mr258876/Project-Puncher/Project_HolePuncher/src/PuncherMotors.cpp

#include "PuncherMotors.h"

MotorController *controller_X = NULL;
MotorController *controller_Y = NULL;
MotorController *controller_Z = NULL;

PositionSensor *sensor_X = NULL;
PositionSensor *sensor_Y = NULL;
PositionSensor *sensor_Z = NULL;
