mr258876/Project-Puncher/Project_HolePuncher/include/PuncherSchedulerAbst.h

#ifndef _PUNCHERSCHEDULERABST_H_
#define _PUNCHERSCHEDULERABST_H_

#include "PuncherSchedulerTyping.h"
#include "PuncherEvents.h"
#include <time.h>

class PuncherSchedulerInterface
{

public:
    virtual int start_workload() = 0;  // handle by queue
    virtual int pause_workload() = 0;  // handle by queue
    virtual int delete_workload() = 0; // handle by queue
    virtual int data_transmit_mode(bool transmit_mode) = 0;
    virtual int feed_paper_mode(bool feed_paper_mode) = 0;
    virtual int add_hole(scheduler_hole_t &h) = 0;
    /* Note: y in mcode is actually Z axis! */
    virtual int add_hold_mcode(int x, int y, int z) = 0;

    virtual int feed_paper(int gear, bool slow_mode) = 0;
    virtual int util_move_X(int dir, bool use_zeroing_conf) = 0; // handle by queue
    virtual int util_move_Y(int dir, bool use_zeroing_conf) = 0; // handle by queue
    virtual int read_sg_result(int axis) = 0;                    // handle by queue
    virtual int start_auto_zeroing(int axis) = 0;                // handle by queue
    virtual int start_encoder_calibrate(int axis) = 0;           // handle by queue

    virtual unsigned int set_status(unsigned int status_code) = 0;
    virtual unsigned int get_status() = 0;
    virtual time_t get_ETA() = 0;
    virtual void set_setting_value(puncher_event_setting_change_t *evt) = 0; // handle by queue
    virtual void get_setting_values(void *ui) = 0;
    virtual void get_status(void *ui) = 0;
};

#endif
