mr258876/Project-Puncher/Project_HolePuncher/include/PuncherSemaphore.h

#ifndef _PUNCHERSEMAPHORE_H_
#define _PUNCHERSEMAPHORE_H_

#include <freertos/FreeRTOS.h>
#include <freertos/semphr.h>

extern SemaphoreHandle_t I2C0Mutex;
extern SemaphoreHandle_t I2C1Mutex;
extern SemaphoreHandle_t SPI2Mutex;
extern SemaphoreHandle_t SPI3Mutex;
extern SemaphoreHandle_t *LCDMutexptr;
extern SemaphoreHandle_t LVGLMutex;
extern SemaphoreHandle_t UART0Mutex;
extern SemaphoreHandle_t UART1Mutex;
extern SemaphoreHandle_t UART2Mutex;
extern SemaphoreHandle_t *DUARTMutex;

#endif  // _PUNCHERSEMAPHORE_H_
