mr258876/Project-Puncher/Project_HolePuncher/src/ui/i18n/lv_i18n.c

#include "./lv_i18n.h"


////////////////////////////////////////////////////////////////////////////////
// Define plural operands
// http://unicode.org/reports/tr35/tr35-numbers.html#Operands

// Integer version, simplified

#define UNUSED(x) (void)(x)

static inline uint32_t op_n(int32_t val) { return (uint32_t)(val < 0 ? -val : val); }
static inline uint32_t op_i(uint32_t val) { return val; }
// always zero, when decimal part not exists.
static inline uint32_t op_v(uint32_t val) { UNUSED(val); return 0;}
static inline uint32_t op_w(uint32_t val) { UNUSED(val); return 0; }
static inline uint32_t op_f(uint32_t val) { UNUSED(val); return 0; }
static inline uint32_t op_t(uint32_t val) { UNUSED(val); return 0; }

static lv_i18n_phrase_t en_us_singulars[] = {
    {"Operational Speed (mm/s)", "Operational\nSpeed (mm/s)"},
    {"_length_type_options", "Diameter\nPerimeter"},
    {"Operational Current (mA)", "Operational\nCurrent (mA)"},
    {"_idle_behavior_options", "Keep Current\nReduce Current\nCut Power"},
    {"Auto Zeroing", "Auto\nZeroing"},
    {"Auto Zeroing on Boot", "Auto Zeroing\non Boot"},
    {"Reverse Zeroing Direction", "Reverse\nZeroing Dir."},
    {"Zeroing Torch Threshold", "Zeroing Torch\nThreshold"},
    {"Zeroing Speed (mm/s)", "Zeroing Speed\n(mm/s)"},
    {"Zeroing Position (mm)", "Zeroing Position\n(mm)"},
    {"Move Axis", "Move\nAxis"},
    {"SG Result", "SG Result: -1"},
    {"_sg_result_fmt", "SG Result: %d"},
    {"_move_axis_speed_options", "Operational\nZeroing"},
    {"_motor_voltage_options", "5V\n9V\n12V\n15V\n20V"},
    {"_language_options", "English\n简体中文"},
    {"Move Target Beats", "Move\nto Target"},
    {"Measured Residual (mm)", "Measured\nResidual (mm)"},
    {"Punch Depth (mm)", "Punch Depth\n(mm)"},
    {"_encoder_type_options", "AS5600"},
    {"Auto Calibrate", "Auto\nCalibrate"},
    {"_version", "Firmware Version\n%s"},
    {"_about_page_author", "@mr258876\n2023-2024\nPlease star this project on Github!"},
    {"_tips_1", "tips: You could send mission by USB, Wi-Fi or Bluetooth."},
    {"_driver_err_template", "Driver error on axis %s"},
    {"_motor_err_template", "Motor error on axis %s"},
    {"_power_err_template", "Failed to acquire votage."},
    {"_driver_err_template_tips", "Driver error on axis %s. Please check driver installation."},
    {"_motor_err_template_tips", "Motor error on axis %s. Please check cable connections."},
    {"_power_err_template_tips", "Failed to acquire votage. Please check compatibility of your power supply."},
    {NULL, NULL} // End mark
};



static uint8_t en_us_plural_fn(int32_t num)
{
    uint32_t n = op_n(num); UNUSED(n);
    uint32_t i = op_i(n); UNUSED(i);
    uint32_t v = op_v(n); UNUSED(v);

    if ((i == 1 && v == 0)) return LV_I18N_PLURAL_TYPE_ONE;
    return LV_I18N_PLURAL_TYPE_OTHER;
}

static const lv_i18n_lang_t en_us_lang = {
    .locale_name = "en-US",
    .singulars = en_us_singulars,

    .locale_plural_fn = en_us_plural_fn
};

static lv_i18n_phrase_t zh_cn_singulars[] = {
    {"Status", "状态"},
    {"ETA", "预计剩余时间"},
    {"Feed", "进纸"},
    {"Slow", "慢速"},
    {"Setting", "设置"},
    {"Info", "信息"},
    {"Warning", "警告"},
    {"Error", "错误"},
    {"Error Occured", "有错误发生"},
    {"Back", "返回"},
    {"About", "关于"},
    {"STOP", "停止"},
    {"Connectivity", "连接"},
    {"Motors", "电机"},
    {"Display", "显示"},
    {"Disp.", "显示"},
    {"Others", "其他"},
    {"Brightness", "亮度"},
    {"BLE", "蓝牙"},
    {"X Axis", "X轴"},
    {"Y Axis", "Y轴"},
    {"Z Axis", "Z轴"},
    {"Mechanical", "机械"},
    {"Lead Length (mm)", "导程长度(mm)"},
    {"Operational Speed (mm/s)", "运行速度(mm/s)"},
    {"Length Type", "长度类型"},
    {"_length_type_options", "直径\n周长"},
    {"Reverse Axis", "反转方向"},
    {"Electrical", "电气"},
    {"Operational Current (mA)", "运行电流(mA)"},
    {"Idle Behavior", "空闲行为"},
    {"_idle_behavior_options", "保持电流\n减小电流\n切断电源"},
    {"Sleep Current (mA)", "睡眠电流(mA)"},
    {"Zeroing", "归位"},
    {"Auto Zeroing", "自动归位"},
    {"Auto Zeroing on Boot", "开机自动归位"},
    {"Reverse Zeroing Direction", "反转归位方向"},
    {"Zeroing Torch Threshold", "归位力矩阈值"},
    {"Zeroing Current (mA)", "归位电流(mA)"},
    {"Zeroing Speed (mm/s)", "归位速度(mm/s)"},
    {"Zeroing Position (mm)", "归位后位置(mm)"},
    {"Execute", "执行"},
    {"Utility", "微调工具"},
    {"Move Axis", "启动电机"},
    {"SG Result", "力矩读数: -1"},
    {"_sg_result_fmt", "力矩读数: %d"},
    {"Speed Type", "速度类型"},
    {"_move_axis_speed_options", "按运行设置\n按归位设置"},
    {"Power", "供电"},
    {"Voltage", "电压"},
    {"Motor Voltage", "电机电压"},
    {"Screen", "屏幕"},
    {"System", "系统"},
    {"Language", "语言"},
    {"_language_options", "English\n简体中文"},
    {"Mcode Tickrate", "Mcode 每小节tick数"},
    {"Calibration", "校准"},
    {"Target Beats", "目标拍数"},
    {"Move Target Beats", "移动至\n目标拍数"},
    {"Measured Beats", "测量拍数"},
    {"Measured Residual (mm)", "测量残差(mm)"},
    {"Punch Depth (mm)", "打孔深度(mm)"},
    {"Idle", "空闲"},
    {"Ready", "就绪"},
    {"Receiving Data", "正在接收数据"},
    {"Encoder", "编码器"},
    {"Use Encoder", "启用编码器"},
    {"Encoder Type", "编码器类型"},
    {"_encoder_type_options", "AS5600"},
    {"Auto Calibrate", "自动校准"},
    {"Please Wait", "请稍候"},
    {"Axis Zeroing...", "正在自动归位..."},
    {"Transmitting Data...", "正在传输数据..."},
    {"_version", "固件版本\n%s"},
    {"_about_page_author", "@mr258876\n2023-2024\n请在 Github 上为该项目点 Star !"},
    {"_tips_1", "提示: 您可以通过USB, 无线网络或蓝牙传输作业任务。"},
    {"_driver_err_template", "%s 轴驱动器异常"},
    {"_motor_err_template", "%s 轴电机异常"},
    {"_power_err_template", "请求电压失败"},
    {"_driver_err_template_tips", "%s 轴驱动器异常。请检查驱动器是否已正确安装。"},
    {"_motor_err_template_tips", "%s 轴电机异常。请检查电机线缆是否断开。"},
    {"_power_err_template_tips", "请求电压失败。请检查电源兼容性。"},
    {"_driver_err_template_cpp", "轴驱动器异常"},
    {"_motor_err_template_cpp", "轴电机异常"},
    {"_driver_err_template_cpp_tips", "轴驱动器异常。请检查驱动器是否已正确安装。"},
    {"_motor_err_template_cpp_tips", "轴电机异常。请检查电机线缆是否断开。"},
    {NULL, NULL} // End mark
};



static uint8_t zh_cn_plural_fn(int32_t num)
{



    return LV_I18N_PLURAL_TYPE_OTHER;
}

static const lv_i18n_lang_t zh_cn_lang = {
    .locale_name = "zh-CN",
    .singulars = zh_cn_singulars,

    .locale_plural_fn = zh_cn_plural_fn
};

const lv_i18n_language_pack_t lv_i18n_language_pack[] = {
    &en_us_lang,
    &zh_cn_lang,
    NULL // End mark
};

////////////////////////////////////////////////////////////////////////////////


// Internal state
static const lv_i18n_language_pack_t * current_lang_pack;
static const lv_i18n_lang_t * current_lang;


/**
 * Reset internal state. For testing.
 */
void __lv_i18n_reset(void)
{
    current_lang_pack = NULL;
    current_lang = NULL;
}

/**
 * Set the languages for internationalization
 * @param langs pointer to the array of languages. (Last element has to be `NULL`)
 */
int lv_i18n_init(const lv_i18n_language_pack_t * langs)
{
    if(langs == NULL) return -1;
    if(langs[0] == NULL) return -1;

    current_lang_pack = langs;
    current_lang = langs[0];     /*Automatically select the first language*/
    return 0;
}

/**
 * Change the localization (language)
 * @param l_name name of the translation locale to use. E.g. "en-GB"
 */
int lv_i18n_set_locale(const char * l_name)
{
    if(current_lang_pack == NULL) return -1;

    uint16_t i;

    for(i = 0; current_lang_pack[i] != NULL; i++) {
        // Found -> finish
        if(strcmp(current_lang_pack[i]->locale_name, l_name) == 0) {
            current_lang = current_lang_pack[i];
            return 0;
        }
    }

    return -1;
}


static const char * __lv_i18n_get_text_core(lv_i18n_phrase_t * trans, const char * msg_id)
{
    uint16_t i;
    for(i = 0; trans[i].msg_id != NULL; i++) {
        if(strcmp(trans[i].msg_id, msg_id) == 0) {
            /*The msg_id has found. Check the translation*/
            if(trans[i].translation) return trans[i].translation;
        }
    }

    return NULL;
}


/**
 * Get the translation from a message ID
 * @param msg_id message ID
 * @return the translation of `msg_id` on the set local
 */
const char * lv_i18n_get_text(const char * msg_id)
{
    if(current_lang == NULL) return msg_id;

    const lv_i18n_lang_t * lang = current_lang;
    const void * txt;

    // Search in current locale
    if(lang->singulars != NULL) {
        txt = __lv_i18n_get_text_core(lang->singulars, msg_id);
        if (txt != NULL) return txt;
    }

    // Try to fallback
    if(lang == current_lang_pack[0]) return msg_id;
    lang = current_lang_pack[0];

    // Repeat search for default locale
    if(lang->singulars != NULL) {
        txt = __lv_i18n_get_text_core(lang->singulars, msg_id);
        if (txt != NULL) return txt;
    }

    return msg_id;
}

/**
 * Get the translation from a message ID and apply the language's plural rule to get correct form
 * @param msg_id message ID
 * @param num an integer to select the correct plural form
 * @return the translation of `msg_id` on the set local
 */
const char * lv_i18n_get_text_plural(const char * msg_id, int32_t num)
{
    if(current_lang == NULL) return msg_id;

    const lv_i18n_lang_t * lang = current_lang;
    const void * txt;
    lv_i18n_plural_type_t ptype;

    // Search in current locale
    if(lang->locale_plural_fn != NULL) {
        ptype = lang->locale_plural_fn(num);

        if(lang->plurals[ptype] != NULL) {
            txt = __lv_i18n_get_text_core(lang->plurals[ptype], msg_id);
            if (txt != NULL) return txt;
        }
    }

    // Try to fallback
    if(lang == current_lang_pack[0]) return msg_id;
    lang = current_lang_pack[0];

    // Repeat search for default locale
    if(lang->locale_plural_fn != NULL) {
        ptype = lang->locale_plural_fn(num);

        if(lang->plurals[ptype] != NULL) {
            txt = __lv_i18n_get_text_core(lang->plurals[ptype], msg_id);
            if (txt != NULL) return txt;
        }
    }

    return msg_id;
}

/**
 * Get the name of the currently used locale.
 * @return name of the currently used locale. E.g. "en-GB"
 */
const char * lv_i18n_get_current_locale(void)
{
    if(!current_lang) return NULL;
    return current_lang->locale_name;
}
