mr258876/Project-Puncher/Project_HolePuncher/src/ui/ui_setting_menu.h

#ifndef _UI_SETTING_MENU_H_
#define _UI_SETTING_MENU_H_

#include "lvgl.h"

extern lv_obj_t * ui_setting_root_page;
extern lv_obj_t * ui_setting_wifi_page;
extern lv_obj_t * ui_setting_ble_page;
extern lv_obj_t * ui_setting_usb_page;
extern lv_obj_t * ui_setting_mcode_page;
extern lv_obj_t * ui_setting_x_axis_page;
extern lv_obj_t * ui_setting_y_axis_page;
extern lv_obj_t * ui_setting_z_axis_page;
extern lv_obj_t * ui_setting_power_page;
extern lv_obj_t * ui_setting_display_page;
extern lv_obj_t * ui_setting_about_page;

extern lv_obj_t * ui_setting_wifi_switch;

extern lv_obj_t * ui_setting_ble_switch;

extern lv_obj_t * ui_setting_usb_switch;

extern lv_obj_t * ui_setting_usb_mcode_tick_rate;

extern lv_obj_t * ui_setting_x_lead_length;
extern lv_obj_t * ui_setting_x_operational_speed;
extern lv_obj_t * ui_setting_x_length_type;
extern lv_obj_t * ui_setting_x_reverse_axis;
extern lv_obj_t * ui_setting_x_operational_current;
extern lv_obj_t * ui_setting_x_idle_behavior;
extern lv_obj_t * ui_setting_x_sleep_current;
extern lv_obj_t * ui_setting_x_auto_zreoing;
extern lv_obj_t * ui_setting_x_zreoing_reverse_dir;
extern lv_obj_t * ui_setting_x_zeroing_torch_thres;
extern lv_obj_t * ui_setting_x_zeroing_current;
extern lv_obj_t * ui_setting_x_zeroing_speed;
extern lv_obj_t * ui_setting_x_zeroing_position;
extern lv_obj_t * ui_setting_x_zeroing_start;
extern lv_obj_t * ui_setting_x_util_move_left;
extern lv_obj_t * ui_setting_x_util_move_right;
extern lv_obj_t * ui_setting_x_util_sg_result;
extern lv_obj_t * ui_setting_x_util_speed_type;

extern lv_obj_t * ui_setting_y_lead_length;
extern lv_obj_t * ui_setting_y_operational_speed;
extern lv_obj_t * ui_setting_y_length_type;
extern lv_obj_t * ui_setting_y_reverse_axis;
extern lv_obj_t * ui_setting_y_punch_depth;
extern lv_obj_t * ui_setting_y_operational_current;
extern lv_obj_t * ui_setting_y_idle_behavior;
extern lv_obj_t * ui_setting_y_sleep_current;
extern lv_obj_t * ui_setting_y_auto_zreoing;
extern lv_obj_t * ui_setting_y_zreoing_reverse_dir;
extern lv_obj_t * ui_setting_y_zeroing_torch_thres;
extern lv_obj_t * ui_setting_y_zeroing_current;
extern lv_obj_t * ui_setting_y_zeroing_speed;
extern lv_obj_t * ui_setting_y_zeroing_position;
extern lv_obj_t * ui_setting_y_zeroing_start;
extern lv_obj_t * ui_setting_y_util_move_up;
extern lv_obj_t * ui_setting_y_util_move_down;
extern lv_obj_t * ui_setting_y_util_sg_result;
extern lv_obj_t * ui_setting_y_util_speed_type;

extern lv_obj_t * ui_setting_z_lead_length;
extern lv_obj_t * ui_setting_z_operational_speed;
extern lv_obj_t * ui_setting_z_length_type;
extern lv_obj_t * ui_setting_z_reverse_axis;
extern lv_obj_t * ui_setting_z_operational_current;
extern lv_obj_t * ui_setting_z_idle_behavior;
extern lv_obj_t * ui_setting_z_sleep_current;
extern lv_obj_t * ui_setting_z_cali_target;
extern lv_obj_t * ui_setting_z_cali_start_move;
extern lv_obj_t * ui_setting_z_cali_measure;
extern lv_obj_t * ui_setting_z_cali_residual;
extern lv_obj_t * ui_setting_z_encoder_switch;
extern lv_obj_t * ui_setting_z_encoder_type;
extern lv_obj_t * ui_setting_z_encoder_calibrate;

extern lv_obj_t * ui_setting_power_voltage;

extern lv_obj_t * ui_setting_display_brightness;
extern lv_obj_t * ui_setting_display_language;

#endif
